Makerfabs/ESP32S3_2.13_Quad-Color_Eink/example/EPD_Pose_Display/image1.bmp

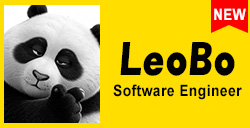
example/EPD_Pose_Display/image1.bmp
