Makerfabs/ESP32S3_2.13_Quad-Color_Eink/example/EPD_Pose_Display/Display_EPD_W21.h

#ifndef _DISPLAY_EPD_W21_H_
#define _DISPLAY_EPD_W21_H_

#define EPD_WIDTH   128
#define EPD_HEIGHT  250
#define EPD_ARRAY  EPD_WIDTH*EPD_HEIGHT/4  

//2bit
#define black   0x00	/// 00
#define white   0x01	///	01
#define yellow  0x02	///	10
#define red     0x03	///	11



//EPD
void EPD_init(void);
void PIC_display (const unsigned char* picData);
void EPD_sleep(void);
void EPD_update(void);
void lcd_chkstatus(void);

void Display_All_Black(void);
void Display_All_White(void);
void Display_All_Yellow(void);
void Display_All_Red(void);
void EPD_init_Fast(void);
void Acep_color(unsigned char color);

#endif
/***********************************************************
						end file
***********************************************************/
